Fillygons/fillygons/src/rhombus.scad

use <_fillygon.scad>

render() fillygon([acos(1 / 3), 180 - acos(1 / 3), acos(1 / 3)]);
