Fillygons/fillygons/src/tests/1-expected.png

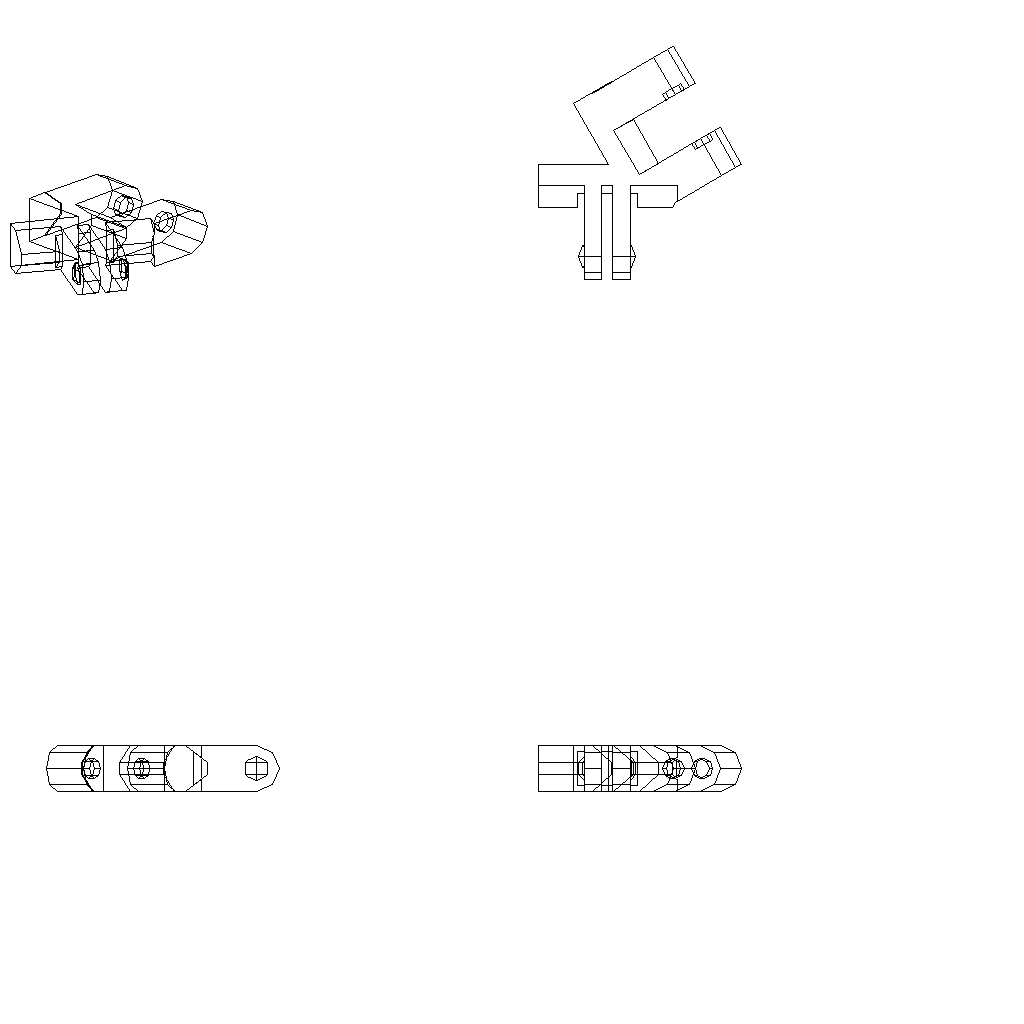
src/tests/1-expected.png
